twlostow/dsi-shield/hdl/rtl/hpdmc/hpdmc.v

/*
 * Milkymist SoC
 * Copyright (C) 2007, 2008, 2009, 2011 Sebastien Bourdeauducq
 *
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
 * You should have received a copy of the GNU General Public License
 * along with this program.  If not, see <http://www.gnu.org/licenses/>.
 */

module hpdmc #(
	       parameter csr_addr = 4'h0,
	       /*
	        * The depth of the SDRAM array, in bytes.
	        * Capacity (in bytes) is 2^sdram_depth.
	        */
	       parameter sdram_depth = 25,

	       /*
	        * The number of column address bits of the SDRAM.
	        */
	       parameter sdram_columndepth = 10,

               parameter data_delay = 0,
               parameter dqs_delay = 0,
	       parameter clock_delay = 0,
	       parameter addr_delay = 0
               ) (
	input 			sys_clk,
	input 			sys_clk_n,
	input 			sys_rst,
	
	/* Control interface */
	input [13:0] 		csr_a,
	input 			csr_we,
	input [31:0] 		csr_di,
	output [31:0] 		csr_do,
	
	/* Simple FML 4x64 interface to the memory contents */
	input [sdram_depth-1:0] fml_adr,
	input 			fml_stb,
	input 			fml_we,
	output 			fml_eack,
        output reg 		fml_ack,
	input [3:0] 		fml_sel,
	input [31:0] 		fml_di,
	output [31:0] 		fml_do,
	
	/* SDRAM interface.
	 * The SDRAM clock should be driven synchronously to the system clock.
	 * It is not generated inside this core so you can take advantage of
	 * architecture-dependent clocking resources to generate a clean
	 * differential clock.
	 */

	output 			sdram_clk_p,
	output 			sdram_clk_n,
	output 			sdram_cke,
	output 			sdram_cs_n,
	output 			sdram_we_n,
	output 			sdram_cas_n,
	output 			sdram_ras_n,
	output [12:0] 		sdram_adr,
	output [1:0] 		sdram_ba,
	
	output [1:0] 		sdram_dm,
	inout [15:0] 		sdram_dq,
	inout [1:0] 		sdram_dqs
);

/* Register all control signals. */
   wire 			sdram_cke_r;
   wire 			sdram_cs_n_r;
   wire 			sdram_we_n_r;
   wire 			sdram_cas_n_r;
   wire 			sdram_ras_n_r;
   wire [12:0] 			sdram_adr_r;
   wire [1:0] 			sdram_ba_r;

   reg 			sdram_cke_predelay;
   reg 			sdram_cs_n_predelay;
   reg 			sdram_we_n_predelay;
   reg 			sdram_cas_n_predelay;
   reg 			sdram_ras_n_predelay;
   reg [12:0] 			sdram_adr_predelay;
   reg [1:0] 			sdram_ba_predelay;

/* -----\/----- EXCLUDED -----\/-----
   always @(posedge sys_clk) begin
      sdram_cke_predelay <= sdram_cke_r;
      sdram_cs_n_predelay <= sdram_cs_n_r;
      sdram_we_n_predelay <= sdram_we_n_r;
      sdram_cas_n_predelay <= sdram_cas_n_r;
      sdram_ras_n_predelay <= sdram_ras_n_r;
      sdram_ba_predelay <= sdram_ba_r;
      sdram_adr_predelay <= sdram_adr_r;
   end
 -----/\----- EXCLUDED -----/\----- */

   hpdmc_ofd
     #(
       .g_width(20),
       .g_delay(addr_delay)
       )
   delay_ctrl 
     (
      .clk_p_i(sys_clk),
      .clk_n_i(sys_clk_n),
      
      .in_i( {sdram_cke_r, 
	      sdram_cs_n_r,
	      sdram_we_n_r,
	      sdram_cas_n_r,
	      sdram_ras_n_r,
	      sdram_ba_r,
	      sdram_adr_r } ),
      .out_o( {sdram_cke, 
	       sdram_cs_n,
	       sdram_we_n,
	       sdram_cas_n,
	       sdram_ras_n,
	       sdram_ba,
	       sdram_adr } ) 
      );
       

/* Mux the control signals according to the "bypass" selection.
 * CKE always comes from the control interface.
 */
wire bypass;

wire sdram_cs_n_bypass;
wire sdram_we_n_bypass;
wire sdram_cas_n_bypass;
wire sdram_ras_n_bypass;
wire [12:0] sdram_adr_bypass;
wire [1:0] sdram_ba_bypass;

wire sdram_cs_n_mgmt;
wire sdram_we_n_mgmt;
wire sdram_cas_n_mgmt;
wire sdram_ras_n_mgmt;
wire [12:0] sdram_adr_mgmt;
wire [1:0] sdram_ba_mgmt;

assign sdram_cs_n_r = bypass ? sdram_cs_n_bypass : sdram_cs_n_mgmt;
assign sdram_we_n_r = bypass ? sdram_we_n_bypass : sdram_we_n_mgmt;
assign sdram_cas_n_r = bypass ? sdram_cas_n_bypass : sdram_cas_n_mgmt;
assign sdram_ras_n_r = bypass ? sdram_ras_n_bypass : sdram_ras_n_mgmt;
assign sdram_adr_r = bypass ? sdram_adr_bypass : sdram_adr_mgmt;
assign sdram_ba_r = bypass ? sdram_ba_bypass : sdram_ba_mgmt;

/* Control interface */
wire sdram_rst;

wire [2:0] tim_rp;
wire [2:0] tim_rcd;
wire tim_cas;
wire [10:0] tim_refi;
wire [3:0] tim_rfc;
wire [1:0] tim_wr;

wire idelay_rst;
wire idelay_ce;
wire idelay_inc;
wire idelay_cal;

hpdmc_ctlif #(
	.csr_addr(csr_addr)
) ctlif (
	.sys_clk(sys_clk),
	.sys_rst(sys_rst),
	
	.csr_a(csr_a),
	.csr_we(csr_we),
	.csr_di(csr_di),
	.csr_do(csr_do),
	
	.bypass(bypass),
	.sdram_rst(sdram_rst),
	
	.sdram_cke(sdram_cke_r),
	.sdram_cs_n(sdram_cs_n_bypass),
	.sdram_we_n(sdram_we_n_bypass),
	.sdram_cas_n(sdram_cas_n_bypass),
	.sdram_ras_n(sdram_ras_n_bypass),
	.sdram_adr(sdram_adr_bypass),
	.sdram_ba(sdram_ba_bypass),
	
	.tim_rp(tim_rp),
	.tim_rcd(tim_rcd),
	.tim_cas(tim_cas),
	.tim_refi(tim_refi),
	.tim_rfc(tim_rfc),
	.tim_wr(tim_wr),
	
	.idelay_rst(idelay_rst),
	.idelay_ce(idelay_ce),
	.idelay_inc(idelay_inc),
	.idelay_cal(idelay_cal)
);

/* SDRAM management unit */
wire read;
wire write;
wire [3:0] concerned_bank;
wire read_safe;
wire write_safe;
wire [3:0] precharge_safe;

  
   wire    eack;
   reg  eack_d, eack_d1;

   always@(posedge sys_clk)
     begin
	eack_d <= eack;
	eack_d1 <= eack_d;
     end
   
   
   assign fml_eack = (fml_we ? eack : eack_d1 );

   

hpdmc_mgmt #(
	.sdram_depth(sdram_depth),
	.sdram_columndepth(sdram_columndepth)
) mgmt (
	.sys_clk(sys_clk),
	.sdram_rst(sdram_rst),
	
	.tim_rp(tim_rp),
	.tim_rcd(tim_rcd),
	.tim_refi(tim_refi),
	.tim_rfc(tim_rfc),
	
	.stb(fml_stb),
	.we(fml_we),
	.address(fml_adr[sdram_depth-1:2]),
	.ack(eack),
	
	.read(read),
	.write(write),
	.concerned_bank(concerned_bank),
	.read_safe(read_safe),
	.write_safe(write_safe),
	.precharge_safe(precharge_safe),
	
	.sdram_cs_n(sdram_cs_n_mgmt),
	.sdram_we_n(sdram_we_n_mgmt),
	.sdram_cas_n(sdram_cas_n_mgmt),
	.sdram_ras_n(sdram_ras_n_mgmt),
	.sdram_adr(sdram_adr_mgmt),
	.sdram_ba(sdram_ba_mgmt)
);

/* Data path controller */
wire direction;

hpdmc_datactl datactl(
	.sys_clk(sys_clk),
	.sdram_rst(sdram_rst),
	
	.read(read),
	.write(write),
	.concerned_bank(concerned_bank),
	.read_safe(read_safe),
	.write_safe(write_safe),
	.precharge_safe(precharge_safe),
	
	.direction(direction),
	
	.tim_cas(tim_cas),
	.tim_wr(tim_wr)
);

/* Data path */
hpdmc_ddrio #(
              .data_delay(data_delay),
              .dqs_delay(dqs_delay),
	      .clock_delay(clock_delay)
) drio (
	.sys_clk(sys_clk),
	.sys_clk_n(sys_clk_n),

	.direction(direction),
	/* Bit meaning is the opposite between
	 * the FML selection signal and SDRAM DM pins.
	 */
	.mo(~fml_sel),
	.do(fml_di),
	.di(fml_do),
	
	.sdram_dm(sdram_dm),
	.sdram_dq(sdram_dq),
	.sdram_dqs(sdram_dqs),
	.sdram_clk_p(sdram_clk_p),
        .sdram_clk_n(sdram_clk_n),
        
	.idelay_rst(idelay_rst),
	.idelay_ce(idelay_ce),
	.idelay_inc(idelay_inc),
	.idelay_cal(idelay_cal)
);

endmodule
