twlostow/dsi-shield/hdl/rtl/hpdmc/spartan6/hpdmc_idelay32.v

/*
 * Milkymist SoC
 * Copyright (C) 2007, 2008, 2009 Sebastien Bourdeauducq
 *
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
 * You should have received a copy of the GNU General Public License
 * along with this program.  If not, see <http://www.gnu.org/licenses/>.
 */

module hpdmc_idelay32(
	input [31:0] IDATAIN,
	output [31:0] DATAOUT,
	input INC,
	input CE,
	input RST,
	input CAL,
	input CLK,
	input IOCLK0,
	input IOCLK1
);

IODELAY2 #(
	.DELAY_SRC("IDATAIN"),
	.IDELAY_TYPE("VARIABLE_FROM_ZERO"),
	.DATA_RATE("DDR")
) idelay0 (
	.IDATAIN(IDATAIN[0]),
	.DATAOUT(DATAOUT[0]),
	.INC(INC),
	.CE(CE),
	.RST(RST),
	.CLK(CLK),
	.IOCLK0(IOCLK0),
	.IOCLK1(IOCLK1),
	.ODATAIN(1'b0),
	.CAL(CAL),
	.T(1'b1)
);
IODELAY2 #(
	.DELAY_SRC("IDATAIN"),
	.IDELAY_TYPE("VARIABLE_FROM_ZERO"),
	.DATA_RATE("DDR")
) idelay1 (
	.IDATAIN(IDATAIN[1]),
	.DATAOUT(DATAOUT[1]),
	.INC(INC),
	.CE(CE),
	.RST(RST),
	.CLK(CLK),
	.IOCLK0(IOCLK0),
	.IOCLK1(IOCLK1),
	.ODATAIN(1'b0),
	.CAL(CAL),
	.T(1'b1)
);
IODELAY2 #(
	.DELAY_SRC("IDATAIN"),
	.IDELAY_TYPE("VARIABLE_FROM_ZERO"),
	.DATA_RATE("DDR")
) idelay2 (
	.IDATAIN(IDATAIN[2]),
	.DATAOUT(DATAOUT[2]),
	.INC(INC),
	.CE(CE),
	.RST(RST),
	.CLK(CLK),
	.IOCLK0(IOCLK0),
	.IOCLK1(IOCLK1),
	.ODATAIN(1'b0),
	.CAL(CAL),
	.T(1'b1)
);
IODELAY2 #(
	.DELAY_SRC("IDATAIN"),
	.IDELAY_TYPE("VARIABLE_FROM_ZERO"),
	.DATA_RATE("DDR")
) idelay3 (
	.IDATAIN(IDATAIN[3]),
	.DATAOUT(DATAOUT[3]),
	.INC(INC),
	.CE(CE),
	.RST(RST),
	.CLK(CLK),
	.IOCLK0(IOCLK0),
	.IOCLK1(IOCLK1),
	.ODATAIN(1'b0),
	.CAL(CAL),
	.T(1'b1)
);
IODELAY2 #(
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
);
IODELAY2 #(
	.DELAY_SRC("IDATAIN"),
	.IDELAY_TYPE("VARIABLE_FROM_ZERO"),
	.DATA_RATE("DDR")
) idelay30 (
	.IDATAIN(IDATAIN[30]),
	.DATAOUT(DATAOUT[30]),
	.INC(INC),
	.CE(CE),
	.RST(RST),
	.CLK(CLK),
	.IOCLK0(IOCLK0),
	.IOCLK1(IOCLK1),
	.ODATAIN(1'b0),
	.CAL(CAL),
	.T(1'b1)
);
IODELAY2 #(
	.DELAY_SRC("IDATAIN"),
	.IDELAY_TYPE("VARIABLE_FROM_ZERO"),
	.DATA_RATE("DDR")
) idelay31 (
	.IDATAIN(IDATAIN[31]),
	.DATAOUT(DATAOUT[31]),
	.INC(INC),
	.CE(CE),
	.RST(RST),
	.CLK(CLK),
	.IOCLK0(IOCLK0),
	.IOCLK1(IOCLK1),
	.ODATAIN(1'b0),
	.CAL(CAL),
	.T(1'b1)
);

endmodule
