twlostow/dsi-shield/hdl/ip_cores/local/xwb_dpram.vhd

-------------------------------------------------------------------------------
-- Title      : Dual-port RAM for WR core
-- Project    : WhiteRabbit
-------------------------------------------------------------------------------
-- File       : wrc_dpram.vhd
-- Author     : Grzegorz Daniluk
-- Company    : Elproma, CERN
-- Created    : 2011-02-15
-- Last update: 2013-09-11
-- Platform   : FPGA-generics
-- Standard   : VHDL '93
-------------------------------------------------------------------------------
-- Description:
--
-- Dual port RAM with wishbone interface
-------------------------------------------------------------------------------
-- Copyright (c) 2011 Grzegorz Daniluk
-------------------------------------------------------------------------------
-- Revisions  :
-- Date        Version  Author          Description
-- 2011-02-15  1.0      greg.d          Created
-- 2011-06-09  1.01     twlostow        Removed unnecessary generics
-- 2011-21-09  1.02     twlostow        Struct-ized version
-------------------------------------------------------------------------------

library ieee;
use ieee.std_logic_1164.all;
use ieee.numeric_std.all;


library work;
use work.genram_pkg.all;
use work.wishbone_pkg.all;

entity xwb_dpram is
  generic(
    g_size                  : natural := 16384;
    g_init_file             : string  := "";
    g_must_have_init_file   : boolean := true;
    g_slave1_interface_mode : t_wishbone_interface_mode;
    g_slave2_interface_mode : t_wishbone_interface_mode;
    g_slave1_granularity    : t_wishbone_address_granularity;
    g_slave2_granularity    : t_wishbone_address_granularity
    );
  port(
    clk_sys_i : in std_logic;
    rst_n_i   : in std_logic;

    slave1_i : in  t_wishbone_slave_in;
    slave1_o : out t_wishbone_slave_out;
    slave2_i : in  t_wishbone_slave_in;
    slave2_o : out t_wishbone_slave_out
    );
end xwb_dpram;

architecture struct of xwb_dpram is

  function f_zeros(size : integer)
    return std_logic_vector is
  begin
    return std_logic_vector(to_unsigned(0, size));
  end f_zeros;


  signal s_wea  : std_logic;
  signal s_web  : std_logic;
  signal s_bwea : std_logic_vector(3 downto 0);
  signal s_bweb : std_logic_vector(3 downto 0);

  signal slave1_in  : t_wishbone_slave_in;
  signal slave1_out : t_wishbone_slave_out;
  signal slave2_in  : t_wishbone_slave_in;
  signal slave2_out : t_wishbone_slave_out;
  
  

  
begin
  U_Adapter1 : wb_slave_adapter
    generic map (
      g_master_use_struct  => true,
      g_master_mode        => g_slave1_interface_mode,
      g_master_granularity => WORD,
      g_slave_use_struct   => true,
      g_slave_mode         => g_slave1_interface_mode,
      g_slave_granularity  => g_slave1_granularity)
    port map (
      clk_sys_i => clk_sys_i,
      rst_n_i   => rst_n_i,
      slave_i   => slave1_i,
      slave_o   => slave1_o,
      master_i  => slave1_out,
      master_o  => slave1_in);

  U_Adapter2 : wb_slave_adapter
    generic map (
      g_master_use_struct  => true,
      g_master_mode        => g_slave2_interface_mode,
      g_master_granularity => WORD,
      g_slave_use_struct   => true,
      g_slave_mode         => g_slave2_interface_mode,
      g_slave_granularity  => g_slave2_granularity)
    port map (
      clk_sys_i => clk_sys_i,
      rst_n_i   => rst_n_i,
      slave_i   => slave2_i,
      slave_o   => slave2_o,
      master_i  => slave2_out,
      master_o  => slave2_in);

  GEN_INITF: if g_init_file /= "" and g_init_file /= "none" generate
    -- Unfortunately stupid ISE has problem with understanding bytesel
    -- description in generic_dpram so it instantiates this using numerous LUTs
    -- for connecting BRAMs and supporting bytesel. When initialization with
    -- file is not needed it's better to use GEN_NO_INITF.
    U_DPRAM : generic_dpram
      generic map(
        -- standard parameters
        g_data_width               => 32,
        g_size                     => g_size,
        g_with_byte_enable         => true,
        g_addr_conflict_resolution => "dont_care",
        g_init_file                => g_init_file,
        g_dual_clock               => false
        )
      port map(
        rst_n_i => rst_n_i,
        -- Port A
        clka_i  => clk_sys_i,
        bwea_i  => s_bwea,
        wea_i   => s_wea,
        aa_i    => slave1_in.adr(f_log2_size(g_size)-1 downto 0),
        da_i    => slave1_in.dat,
        qa_o    => slave1_out.dat,
        -- Port B
        clkb_i  => clk_sys_i,
        bweb_i  => s_bweb,
        web_i   => s_web,
        ab_i    => slave2_in.adr(f_log2_size(g_size)-1 downto 0),
        db_i    => slave2_in.dat,
        qb_o    => slave2_out.dat
        );
  end generate;

  GEN_NO_INITF: if g_init_file = "" or g_init_file = "none" generate
    -- This trick splits ram into four 8-bit blocks of RAM. Now the problem ISE
    -- has with understanding correctly bytesel is bypassed and the
    -- implementation takes almost none LUTs, just BRAMs.
    GEN_BYTESEL: for i in 0 to 3 generate
      U_DPRAM: generic_dpram
        generic map(
          g_data_width               => 8,
          g_size                     => g_size,
          g_with_byte_enable         => false,
          g_addr_conflict_resolution => "dont_care",
          g_init_file                => "",
          g_dual_clock               => false)
      port map(
        rst_n_i => rst_n_i,
        -- Port A
        clka_i  => clk_sys_i,
        wea_i   => s_bwea(i),
        aa_i    => slave1_in.adr(f_log2_size(g_size)-1 downto 0),
        da_i    => slave1_in.dat((i+1)*8-1 downto i*8),
        qa_o    => slave1_out.dat((i+1)*8-1 downto i*8),
        -- Port B
        clkb_i  => clk_sys_i,
        web_i   => s_bweb(i),
        ab_i    => slave2_in.adr(f_log2_size(g_size)-1 downto 0),
        db_i    => slave2_in.dat((i+1)*8-1 downto i*8),
        qb_o    => slave2_out.dat((i+1)*8-1 downto i*8)
        );
    end generate;
  end generate;

  -- I know this looks weird, but otherwise ISE generates distributed RAM instead of block
  -- RAM
  s_bwea <= slave1_in.sel when s_wea = '1' else f_zeros(c_wishbone_data_width/8);
  s_bweb <= slave2_in.sel when s_web = '1' else f_zeros(c_wishbone_data_width/8);

  s_wea <= slave1_in.we and slave1_in.stb and slave1_in.cyc;
  s_web <= slave2_in.we and slave2_in.stb and slave2_in.cyc;

  process(clk_sys_i)
  begin
    if(rising_edge(clk_sys_i)) then
      if(rst_n_i = '0') then
        slave1_out.ack <= '0';
        slave2_out.ack <= '0';
      else
        if(slave1_out.ack = '1' and g_slave1_interface_mode = CLASSIC) then
          slave1_out.ack <= '0';
        else
          slave1_out.ack <= slave1_in.cyc and slave1_in.stb;
        end if;

        if(slave2_out.ack = '1' and g_slave2_interface_mode = CLASSIC) then
          slave2_out.ack <= '0';
        else
          slave2_out.ack <= slave2_in.cyc and slave2_in.stb;
        end if;
      end if;
    end if;
  end process;

  slave1_out.stall <= '0';
  slave2_out.stall <= '0';
  slave1_out.err <= '0';
  slave2_out.err <= '0';
  slave1_out.rty <= '0';
  slave2_out.rty <= '0';
  
end struct;
