twlostow/dsi-shield/hdl/rtl/hpdmc/spartan6/hpdmc_iddr32.v

/*
 * Milkymist SoC
 * Copyright (C) 2007, 2008, 2009, 2010 Sebastien Bourdeauducq
 *
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
 * You should have received a copy of the GNU General Public License
 * along with this program.  If not, see <http://www.gnu.org/licenses/>.
 */

module hpdmc_iddr32 #(
	parameter DDR_ALIGNMENT = "C0",
	parameter INIT_Q0 = 1'b0,
	parameter INIT_Q1 = 1'b0,
	parameter SRTYPE = "ASYNC"
) (
	output [31:0] Q0,
	output [31:0] Q1,
	input C0,
	input C1,
	input CE,
	input [31:0] D,
	input R,
	input S
);

IDDR2 #(
	.DDR_ALIGNMENT(DDR_ALIGNMENT),
	.INIT_Q0(INIT_Q0),
	.INIT_Q1(INIT_Q1),
	.SRTYPE(SRTYPE)
) iddr0 (
	.Q0(Q0[0]),
	.Q1(Q1[0]),
	.C0(C0),
	.C1(C1),
	.CE(CE),
	.D(D[0]),
	.R(R),
	.S(S)
);
IDDR2 #(
	.DDR_ALIGNMENT(DDR_ALIGNMENT),
	.INIT_Q0(INIT_Q0),
	.INIT_Q1(INIT_Q1),
	.SRTYPE(SRTYPE)
) iddr1 (
	.Q0(Q0[1]),
	.Q1(Q1[1]),
	.C0(C0),
	.C1(C1),
	.CE(CE),
	.D(D[1]),
	.R(R),
	.S(S)
);
IDDR2 #(
	.DDR_ALIGNMENT(DDR_ALIGNMENT),
	.INIT_Q0(INIT_Q0),
	.INIT_Q1(INIT_Q1),
	.SRTYPE(SRTYPE)
) iddr2 (
	.Q0(Q0[2]),
	.Q1(Q1[2]),
	.C0(C0),
	.C1(C1),
	.CE(CE),
	.D(D[2]),
	.R(R),
	.S(S)
);
IDDR2 #(
	.DDR_ALIGNMENT(DDR_ALIGNMENT),
	.INIT_Q0(INIT_Q0),
	.INIT_Q1(INIT_Q1),
	.SRTYPE(SRTYPE)
) iddr3 (
	.Q0(Q0[3]),
	.Q1(Q1[3]),
	.C0(C0),
	.C1(C1),
	.CE(CE),
	.D(D[3]),
	.R(R),
	.S(S)
);
IDDR2 #(
	.DDR_ALIGNMENT(DDR_ALIGNMENT),
	.INIT_Q0(INIT_Q0),
	.INIT_Q1(INIT_Q1),
	.SRTYPE(SRTYPE)
) iddr4 (
	.Q0(Q0[4]),
	.Q1(Q1[4]),
	.C0(C0),
	.C1(C1),
	.CE(CE),
	.D(D[4]),
	.R(R),
	.S(S)
);
IDDR2 #(
	.DDR_ALIGNMENT(DDR_ALIGNMENT),
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
	.Q0(Q0[26]),
	.Q1(Q1[26]),
	.C0(C0),
	.C1(C1),
	.CE(CE),
	.D(D[26]),
	.R(R),
	.S(S)
);
IDDR2 #(
	.DDR_ALIGNMENT(DDR_ALIGNMENT),
	.INIT_Q0(INIT_Q0),
	.INIT_Q1(INIT_Q1),
	.SRTYPE(SRTYPE)
) iddr27 (
	.Q0(Q0[27]),
	.Q1(Q1[27]),
	.C0(C0),
	.C1(C1),
	.CE(CE),
	.D(D[27]),
	.R(R),
	.S(S)
);
IDDR2 #(
	.DDR_ALIGNMENT(DDR_ALIGNMENT),
	.INIT_Q0(INIT_Q0),
	.INIT_Q1(INIT_Q1),
	.SRTYPE(SRTYPE)
) iddr28 (
	.Q0(Q0[28]),
	.Q1(Q1[28]),
	.C0(C0),
	.C1(C1),
	.CE(CE),
	.D(D[28]),
	.R(R),
	.S(S)
);
IDDR2 #(
	.DDR_ALIGNMENT(DDR_ALIGNMENT),
	.INIT_Q0(INIT_Q0),
	.INIT_Q1(INIT_Q1),
	.SRTYPE(SRTYPE)
) iddr29 (
	.Q0(Q0[29]),
	.Q1(Q1[29]),
	.C0(C0),
	.C1(C1),
	.CE(CE),
	.D(D[29]),
	.R(R),
	.S(S)
);
IDDR2 #(
	.DDR_ALIGNMENT(DDR_ALIGNMENT),
	.INIT_Q0(INIT_Q0),
	.INIT_Q1(INIT_Q1),
	.SRTYPE(SRTYPE)
) iddr30 (
	.Q0(Q0[30]),
	.Q1(Q1[30]),
	.C0(C0),
	.C1(C1),
	.CE(CE),
	.D(D[30]),
	.R(R),
	.S(S)
);
IDDR2 #(
	.DDR_ALIGNMENT(DDR_ALIGNMENT),
	.INIT_Q0(INIT_Q0),
	.INIT_Q1(INIT_Q1),
	.SRTYPE(SRTYPE)
) iddr31 (
	.Q0(Q0[31]),
	.Q1(Q1[31]),
	.C0(C0),
	.C1(C1),
	.CE(CE),
	.D(D[31]),
	.R(R),
	.S(S)
);

endmodule
