twlostow/dsi-shield/hdl/rtl/hpdmc/hpdmc_ctlif.v

/*
 * Milkymist SoC
 * Copyright (C) 2007, 2008, 2009 Sebastien Bourdeauducq
 *
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
 * You should have received a copy of the GNU General Public License
 * along with this program.  If not, see <http://www.gnu.org/licenses/>.
 */

module hpdmc_ctlif #(
	parameter csr_addr = 4'h0
) (
	input sys_clk,
	input sys_rst,
	
	input [13:0] csr_a,
	input csr_we,
	input [31:0] csr_di,
	output reg [31:0] csr_do,
	
	output reg bypass,
	output reg sdram_rst,
	
	output reg sdram_cke,
	output reg sdram_cs_n,
	output reg sdram_we_n,
	output reg sdram_cas_n,
	output reg sdram_ras_n,
	output reg [12:0] sdram_adr,
	output reg [1:0] sdram_ba,
	
	/* Clocks we must wait following a PRECHARGE command (usually tRP). */
	output reg [2:0] tim_rp,
	/* Clocks we must wait following an ACTIVATE command (usually tRCD). */
	output reg [2:0] tim_rcd,
	/* CAS latency, 0 = 2 */
	output reg tim_cas,
	/* Auto-refresh period (usually tREFI). */
	output reg [10:0] tim_refi,
	/* Clocks we must wait following an AUTO REFRESH command (usually tRFC). */
	output reg [3:0] tim_rfc,
	/* Clocks we must wait following the last word written to the SDRAM (usually tWR). */
	output reg [1:0] tim_wr,
	
	output reg idelay_rst,
	output reg idelay_ce,
	output reg idelay_inc,
	output reg idelay_cal
);

wire csr_selected = csr_a[13:10] == csr_addr;

always @(posedge sys_clk) begin
	if(sys_rst) begin
		csr_do <= 32'd0;
	
		bypass <= 1'b1;
		sdram_rst <= 1'b1;
		
		sdram_cke <= 1'b0;
		sdram_adr <= 13'd0;
		sdram_ba <= 2'd0;
		
		tim_rp <= 3'd2;
		tim_rcd <= 3'd2;
		tim_cas <= 1'b0;
		tim_refi <= 11'd620;
		tim_rfc <= 4'd6;
		tim_wr <= 2'd2;
	   idelay_cal <= 0;
	   
	end else begin
		sdram_cs_n <= 1'b1;
		sdram_we_n <= 1'b1;
		sdram_cas_n <= 1'b1;
		sdram_ras_n <= 1'b1;
		
		idelay_rst <= 1'b0;
		idelay_ce <= 1'b0;
		idelay_inc <= 1'b0;
		
		csr_do <= 32'd0;
		if(csr_selected) begin
			if(csr_we) begin
				case(csr_a[1:0])
					2'b00: begin
						bypass <= csr_di[0];
						sdram_rst <= csr_di[1];
						sdram_cke <= csr_di[2];
					end
					2'b01: begin
						sdram_cs_n <= ~csr_di[0];
						sdram_we_n <= ~csr_di[1];
						sdram_cas_n <= ~csr_di[2];
						sdram_ras_n <= ~csr_di[3];
						sdram_adr <= csr_di[16:4];
						sdram_ba <= csr_di[18:17];
					end
					2'b10: begin
						tim_rp <= csr_di[2:0];
						tim_rcd <= csr_di[5:3];
						tim_cas <= csr_di[6];
						tim_refi <= csr_di[17:7];
						tim_rfc <= csr_di[21:18];
						tim_wr <= csr_di[23:22];
					end
					2'b11: begin
						idelay_rst <= csr_di[0];
						idelay_ce <= csr_di[1];
						idelay_inc <= csr_di[2];
						idelay_cal <= csr_di[3];
					end
				endcase
			end
			case(csr_a[1:0])
				2'b00: csr_do <= {sdram_cke, sdram_rst, bypass};
				2'b01: csr_do <= {sdram_ba, sdram_adr, 4'h0};
				2'b10: csr_do <= {tim_wr, tim_rfc, tim_refi, tim_cas, tim_rcd, tim_rp};
				2'b11: csr_do <= 4'd0;
			endcase
		end
	end
end

endmodule
