twlostow/dsi-shield/hdl/rtl/sysctl/edid_eeprom.v

/*.
 * DSI Shield
 * Copyright (C) 2013-2014 twl <twlostow@printf.cc>
 *
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
 * You should have received a copy of the GNU General Public License
 * along with this program.  If not, see <http://www.gnu.org/licenses/>.
 */


`timescale 1ns/1ns

  module edid_eeprom (
		      input 	  clk_sys_i,
		      input 	  rst_n_i,

		      inout 	  scl_b,
		      inout 	  sda_b,

		      input 	  edid_en_i,
		      input 	  scl_master_i,
		      input 	  sda_master_i,
		      output 	  sda_master_o,
		      

		      input 	  hdmi_p5v_notif_i,
		      output 	  hdmi_hpd_en_o,

		      input [7:0] addr_i,
		      input [7:0] data_i,
		      input 	  wr_i);
      

   parameter g_size = 128;
//   parameter g_init_file = "edid.dat";
   parameter g_address = 7'h50;

   reg [7:0] 		    tx_byte='haa;
   wire [7:0] 		    rx_byte;

   wire 		    scl_edid_en, scl_edid_in, scl_edid_out;
   wire 		    sda_edid_en, sda_edid_in, sda_edid_out;
   
   assign hdmi_hpd_en_o = 1'b1;
   
   gc_i2c_slave #(
		  .g_gf_len(1))
   
   U_I2C_Slave 	      
     (
      .clk_i(clk_sys_i),
      .rst_n_i(rst_n_i),

      .scl_i(scl_edid_in),
      .scl_o(scl_edid_out),
      .scl_en_o(scl_edid_en),
      .sda_i(sda_edid_in),
      .sda_o(sda_edid_out),
      .sda_en_o(sda_edid_en),

      .i2c_addr_i(g_address),
      .ack_i(ack),
      .tx_byte_i(tx_byte),
      .rx_byte_o(rx_byte),

      .i2c_sta_p_o(i2c_start),
      .i2c_sto_p_o(i2c_stop),

      .addr_good_p_o(addr_good_p),
      .r_done_p_o(r_done_p),
      .w_done_p_o(w_done_p),

      .op_o(op)
      );

   reg [7:0] 		    edid[0:g_size-1];

   assign ack = 1;
   
   assign tx_byte_i = 0;


   assign scl_edid_in = edid_en_i ? scl_b : 1'b1;
   assign sda_edid_in = edid_en_i ? sda_b : 1'b1;
   
   
   assign scl_b = edid_en_i ? (scl_edid_en ? scl_edid_out : 1'bz) : ( scl_master_i ? 1'b0 : 1'bz );
   assign sda_b = edid_en_i ? (sda_edid_en ? sda_edid_out : 1'bz) : ( sda_master_i ? 1'b0 : 1'bz );

   assign sda_master_o = sda_b;
   
   reg [7:0] 		    addr=0;

   
   always@(posedge clk_sys_i)
     if(wr_i)
       edid[addr_i] <= data_i;
     else
       tx_byte <= edid[addr];

   always@(posedge clk_sys_i)
     begin
	if(!op && r_done_p)
	  addr <= rx_byte;
	else if (op && w_done_p)
	  addr <= addr + 1;
     end


		 
   
endmodule // edid_eeprom
