twlostow/dsi-shield/hdl/ip_cores/local/Manifest.py

files = ["gc_glitch_filt.vhd",
"gc_i2c_slave.vhd",
"gc_pulse_synchronizer.vhd",
"gc_shiftreg.vhd",
"gc_sync_ffs.vhd",
"gc_sync_register.vhd",
"gencores_pkg.vhd",
"generic_dpram_dualclock.vhd",
"generic_dpram_sameclock.vhd",
"generic_dpram.vhd",
"generic_simple_dpram.vhd",
"generic_spram.vhd",
"genram_pkg.vhd",
"inferred_async_fifo.vhd",
"inferred_sync_fifo.vhd",
"memory_loader_pkg.vhd",
"sdb_rom.vhd",
"simple_uart_pkg.vhd",
"simple_uart_wb.vhd",
"uart_async_rx.vhd",
"uart_async_tx.vhd",
"uart_baud_gen.vhd",
"wb_simple_uart.vhd",
"wishbone_pkg.vhd",
"xwb_crossbar.vhd",
"xwb_register_link.vhd",
"xwb_sdb_crossbar.vhd",
"xwb_simple_uart.vhd",
"generic_sync_fifo.vhd",
"generic_async_fifo.vhd",
"wb_slave_adapter.vhd"];
