twlostow/dsi-shield/hdl/rtl/hpdmc/Manifest.py

files = [
"hpdmc_banktimer.v",
"hpdmc_ctlif.v",
"hpdmc_datactl.v",
"hpdmc_mgmt.v",
"hpdmc.v",
"spartan6/hpdmc_ddrio.v",
"spartan6/hpdmc_iddr16.v",
"spartan6/hpdmc_idelay16.v",
"spartan6/hpdmc_iobuf16.v",
"spartan6/hpdmc_iodelay2.v",
"spartan6/hpdmc_iobuf2.v",
"spartan6/hpdmc_obuft2.v",
"spartan6/hpdmc_oddr2.v",
"spartan6/hpdmc_oddr16.v",
"spartan6/hpdmc_oddr4.v",
"spartan6/hpdmc_iodelay.v",
"spartan6/hpdmc_odelay.v"
];
