twlostow/dsi-shield/software/rev2/memtest.c

/*
 * Copyright (c) 2009-2012, Salvatore Sanfilippo <antirez at gmail dot com>
 * All rights reserved.
 *
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
 * THIS SOFTWARE IS PROVIDED BY THE COPYRIGHT HOLDERS AND CONTRIBUTORS "AS IS"
 * AND ANY EXPRESS OR IMPLIED WARRANTIES, INCLUDING, BUT NOT LIMITED TO, THE
 * IMPLIED WARRANTIES OF MERCHANTABILITY AND FITNESS FOR A PARTICULAR PURPOSE
 * ARE DISCLAIMED. IN NO EVENT SHALL THE COPYRIGHT OWNER OR CONTRIBUTORS BE
 * LIABLE FOR ANY DIRECT, INDIRECT, INCIDENTAL, SPECIAL, EXEMPLARY, OR
 * CONSEQUENTIAL DAMAGES (INCLUDING, BUT NOT LIMITED TO, PROCUREMENT OF
 * SUBSTITUTE GOODS OR SERVICES; LOSS OF USE, DATA, OR PROFITS; OR BUSINESS
 * INTERRUPTION) HOWEVER CAUSED AND ON ANY THEORY OF LIABILITY, WHETHER IN
 * CONTRACT, STRICT LIABILITY, OR TORT (INCLUDING NEGLIGENCE OR OTHERWISE)
 * ARISING IN ANY WAY OUT OF THE USE OF THIS SOFTWARE, EVEN IF ADVISED OF THE
 * POSSIBILITY OF SUCH DAMAGE.
 */

#include <stdlib.h>
#include <stdio.h>
#include <string.h>
#include <assert.h>
#include <limits.h>
#include <errno.h>

#define printf pp_printf

#if (ULONG_MAX == 4294967295UL)
#define MEMTEST_32BIT
#elif (ULONG_MAX == 18446744073709551615ULL)
#define MEMTEST_64BIT
#else
#error "ULONG_MAX value not supported."
#endif

#ifdef MEMTEST_32BIT
#define ULONG_ONEZERO 0xaaaaaaaaUL
#define ULONG_ZEROONE 0x55555555UL
#else
#define ULONG_ONEZERO 0xaaaaaaaaaaaaaaaaUL
#define ULONG_ZEROONE 0x5555555555555555UL
#endif

size_t progress_printed; /* Printed chars in screen-wide progress bar. */
size_t progress_full; /* How many chars to write to fill the progress bar. */

int nSeed = 5323;

static int errors = 0;

void memtest_init(){ errors= 0; }
int rand()
{
    // our initial starting seed is 5323

    // Take the current seed and generate a new value from it
    // Due to our use of large constants and overflow, it would be
    // very hard for someone to predict what the next number is
    // going to be from the previous one.
    nSeed = (8253729 * nSeed + 2396403); 

    // Take the seed and return a value between 0 and 32767
    return nSeed;
}

void memtest_progress_start(char *title, int pass) {
    int j;

    /* Fill with dots. */
    pp_printf("Test %s [pass %d, errors so far: %d]\n", title, pass, errors); /* Print title. */
    progress_printed = 0;
}

void memtest_progress_end(void) {
    pp_printf("\r");
}

void memtest_progress_step(size_t curr, size_t size, char c) {
    pp_printf("%d %%        \r", (curr * 100 )/  size); /* Print title. */

//    size_t chars = ((unsigned long long)curr*progress_full)/size, j;

//    for (j = 0; j < chars-progress_printed; j++) printf("%c",c);
//    progress_printed = chars;
}

/* Test that addressing is fine. Every location is populated with its own
 * address, and finally verified. This test is very fast but may detect
 * ASAP big issues with the memory subsystem. */
void memtest_addressing(unsigned long *l, size_t bytes) {
    unsigned long words = bytes/sizeof(unsigned long);
    unsigned long j, *p;

    /* Fill */
    p = l;
    for (j = 0; j < words; j++) {
        *p = (unsigned long)p;
        p++;
        if ((j & 0xffff) == 0) memtest_progress_step(j,words*2,'A');
    }
    /* Test */
    p = l;
    for (j = 0; j < words; j++) {
        if (*p != (unsigned long)p) {
            printf("\n*** MEMORY ADDRESSING ERROR: %p contains %08x mask %08x\n",
                (void*) p, *p, (*p) ^ (unsigned long)p);
errors++;
	return;
//            for(;;);
        }
        p++;
        if ((j & 0xffff) == 0) memtest_progress_step(j+words,words*2,'A');
    }
}

/* Fill words stepping a single page at every write, so we continue to
 * touch all the pages in the smallest amount of time reducing the
 * effectiveness of caches, and making it hard for the OS to transfer
 * pages on the swap. */
void memtest_fill_random(unsigned long *l, size_t bytes) {
    unsigned long step = 4096/sizeof(unsigned long);
    unsigned long words = bytes/sizeof(unsigned long)/2;
    unsigned long iwords = words/step;  /* words per iteration */
    unsigned long off, w, *l1, *l2;

//    assert((bytes & 4095) == 0);
    for (off = 0; off < step; off++) {
        l1 = l+off;
        l2 = l1+words;
        for (w = 0; w < iwords; w++) {
#ifdef MEMTEST_32BIT
            *l1 = *l2 = ((unsigned long)     (rand()&0xffff)) |
                        (((unsigned long)    (rand()&0xffff)) << 16);
#else
            *l1 = *l2 = ((unsigned long)     (rand()&0xffff)) |
                        (((unsigned long)    (rand()&0xffff)) << 16) |
                        (((unsigned long)    (rand()&0xffff)) << 32) |
                        (((unsigned long)    (rand()&0xffff)) << 48);
#endif
            l1 += step;
            l2 += step;
            if ((w & 0xffff) == 0)
                memtest_progress_step(w+iwords*off,words,'R');
        }
    }
}

/* Like memtest_fill_random() but uses the two specified values to fill
 * memory, in an alternated way (v1|v2|v1|v2|...) */
void memtest_fill_value(unsigned long *l, size_t bytes, unsigned long v1,
                        unsigned long v2, char sym)
{
    unsigned long step = 4096/sizeof(unsigned long);
    unsigned long words = bytes/sizeof(unsigned long)/2;
    unsigned long iwords = words/step;  /* words per iteration */
    unsigned long off, w, *l1, *l2, v;

//    assert((bytes & 4095) == 0);
    for (off = 0; off < step; off++) {
        l1 = l+off;
        l2 = l1+words;
        v = (off & 1) ? v2 : v1;
        for (w = 0; w < iwords; w++) {
#ifdef MEMTEST_32BIT
            *l1 = *l2 = ((unsigned long)     v) |
                        (((unsigned long)    v) << 16);
#else
            *l1 = *l2 = ((unsigned long)     v) |
                        (((unsigned long)    v) << 16) |
                        (((unsigned long)    v) << 32) |
                        (((unsigned long)    v) << 48);
#endif
            l1 += step;
            l2 += step;
            if ((w & 0xffff) == 0)
                memtest_progress_step(w+iwords*off,words,sym);
        }
    }
}

void memtest_compare(unsigned long *l, size_t bytes) {
    unsigned long words = bytes/sizeof(unsigned long)/2;
    unsigned long w, *l1, *l2;

//    assert((bytes & 4095) == 0);
    l1 = l;
    l2 = l1+words;
    for (w = 0; w < words; w++) {
        if (*l1 != *l2) {
            printf("\n*** MEMORY ERROR DETECTED: %p != %p (%08x vs %08x) mask %08x\n",
                (void*)l1, (void*)l2, *l1, *l2, *l1 ^ *l2);
errors++;
	return;
//            for(;;);
        }
        l1 ++;
        l2 ++;
        if ((w & 0xffff) == 0) memtest_progress_step(w,words,'=');
    }
}

void memtest_compare_times(unsigned long *m, size_t bytes, int pass, int times) {
    int j;

    for (j = 0; j < times; j++) {
        memtest_progress_start("Compare",pass);
        memtest_compare(m,bytes);
        memtest_progress_end();
    }
}

void memtest_test(void *buffer, size_t megabytes, int passes) {
    size_t bytes = megabytes*1024*1024;
    unsigned long *m = buffer;
    int pass = 0;

    while (pass != passes) {
        pass++;

        memtest_progress_start("Addressing test",pass);
        memtest_addressing(m,bytes);
        memtest_progress_end();

        memtest_progress_start("Random fill",pass);
        memtest_fill_random(m,bytes);
        memtest_progress_end();
        memtest_compare_times(m,bytes,pass,4);

        memtest_progress_start("Solid fill",pass);
        memtest_fill_value(m,bytes,0,(unsigned long)-1,'S');
        memtest_progress_end();
        memtest_compare_times(m,bytes,pass,4);

        memtest_progress_start("Checkerboard fill",pass);
        memtest_fill_value(m,bytes,ULONG_ONEZERO,ULONG_ZEROONE,'C');
        memtest_progress_end();
        memtest_compare_times(m,bytes,pass,4);
    }
}

void memtest_non_destructive_invert(void *addr, size_t size) {
    volatile unsigned long *p = addr;
    size_t words = size / sizeof(unsigned long);
    size_t j;

    /* Invert */
    for (j = 0; j < words; j++)
        p[j] = ~p[j];
}

void memtest_non_destructive_swap(void *addr, size_t size) {
    volatile unsigned long *p = addr;
    size_t words = size / sizeof(unsigned long);
    size_t j;

    /* Swap */
    for (j = 0; j < words; j += 2) {
        unsigned long a, b;

        a = p[j];
        b = p[j+1];
        p[j] = b;
        p[j+1] = a;
    }
}
